fel88/PanelDriver/docs/photo_2024-02-13_19-51-43.jpg

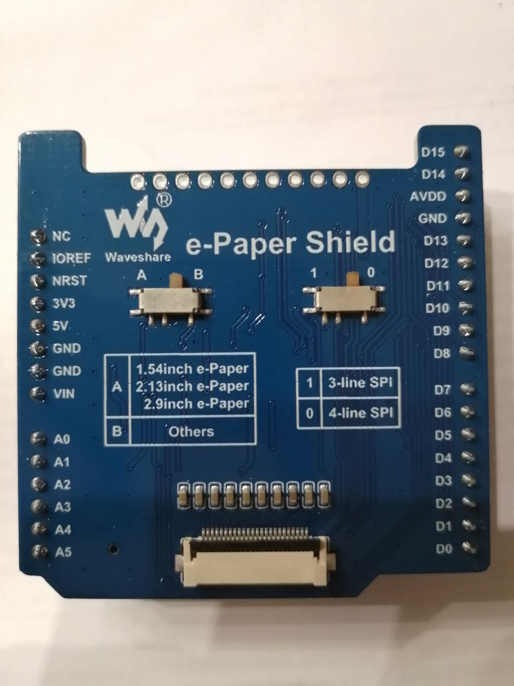
docs/photo_2024-02-13_19-51-43.jpg
